KevinKeWang/tiny_rack/v1/test report/TestReport_SKMW30F-15_and_GST60A15-P1J.csv

time | voltage1 | current1 | power1 | vpp1 | vpp(lpf100k)1 | voltage2 | current2 | power2 | vpp2 | vpp(lpf100k)2
09:01:28 | 11.762 | 0.000 | 0.000 | 55.0 | 18.4 | 12.501 | 0.000 | 0.000 | 77.4 | 8.8
09:01:31 | 11.762 | 0.000 | 0.000 | 59.5 | 18.4 | 12.501 | 0.000 | 0.000 | 77.4 | 7.2
09:01:36 | 11.761 | 0.000 | 0.000 | 59.5 | 17.6 | 12.501 | 0.000 | 0.000 | 91.1 | 7.2
09:01:42 | 11.762 | 0.000 | 0.000 | 64.1 | 18.4 | 12.501 | 0.000 | 0.000 | 77.4 | 8.8
09:01:47 | 11.762 | 0.000 | 0.000 | 59.5 | 18.4 | 12.501 | 0.000 | 0.000 | 77.4 | 8.8
09:01:56 | 11.762 | 0.000 | 0.000 | 55.0 | 18.4 | 12.078 | 0.049 | 0.600 | 77.4 | 7.2
09:02:01 | 11.763 | 0.000 | 0.000 | 64.1 | 18.4 | 12.078 | 0.049 | 0.600 | 86.5 | 8.0
09:02:06 | 11.763 | 0.000 | 0.000 | 59.5 | 22.4 | 12.078 | 0.049 | 0.600 | 91.1 | 8.0
09:02:12 | 11.762 | 0.000 | 0.000 | 64.1 | 19.2 | 12.078 | 0.049 | 0.600 | 86.5 | 8.8
09:02:17 | 11.762 | 0.000 | 0.000 | 55.0 | 21.6 | 12.078 | 0.049 | 0.600 | 91.1 | 8.0
09:02:26 | 11.762 | 0.000 | 0.000 | 55.0 | 16.8 | 12.070 | 0.100 | 1.200 | 86.5 | 7.2
09:02:31 | 11.764 | 0.000 | 0.000 | 59.5 | 17.6 | 12.071 | 0.100 | 1.200 | 86.5 | 7.2
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
